korkin-mv/kch06tc/src/text.h

#ifndef TEXT_H
#define TEXT_H

#include <avr/pgmspace.h>

extern const char text_newline[] PROGMEM;
extern const char text_prompt[] PROGMEM;
extern const char text_delete_in_line[] PROGMEM;
extern const char text_backspace[] PROGMEM;
extern const char text_help[] PROGMEM;
extern const char text_not_found[] PROGMEM;

#endif//TEXT_H
